arvatti/fonte-chaveada-buck/Fonte_Rev1.kicad_sch

## KiCad design Fonte_Rev1.kicad_sch (2026-03-06)

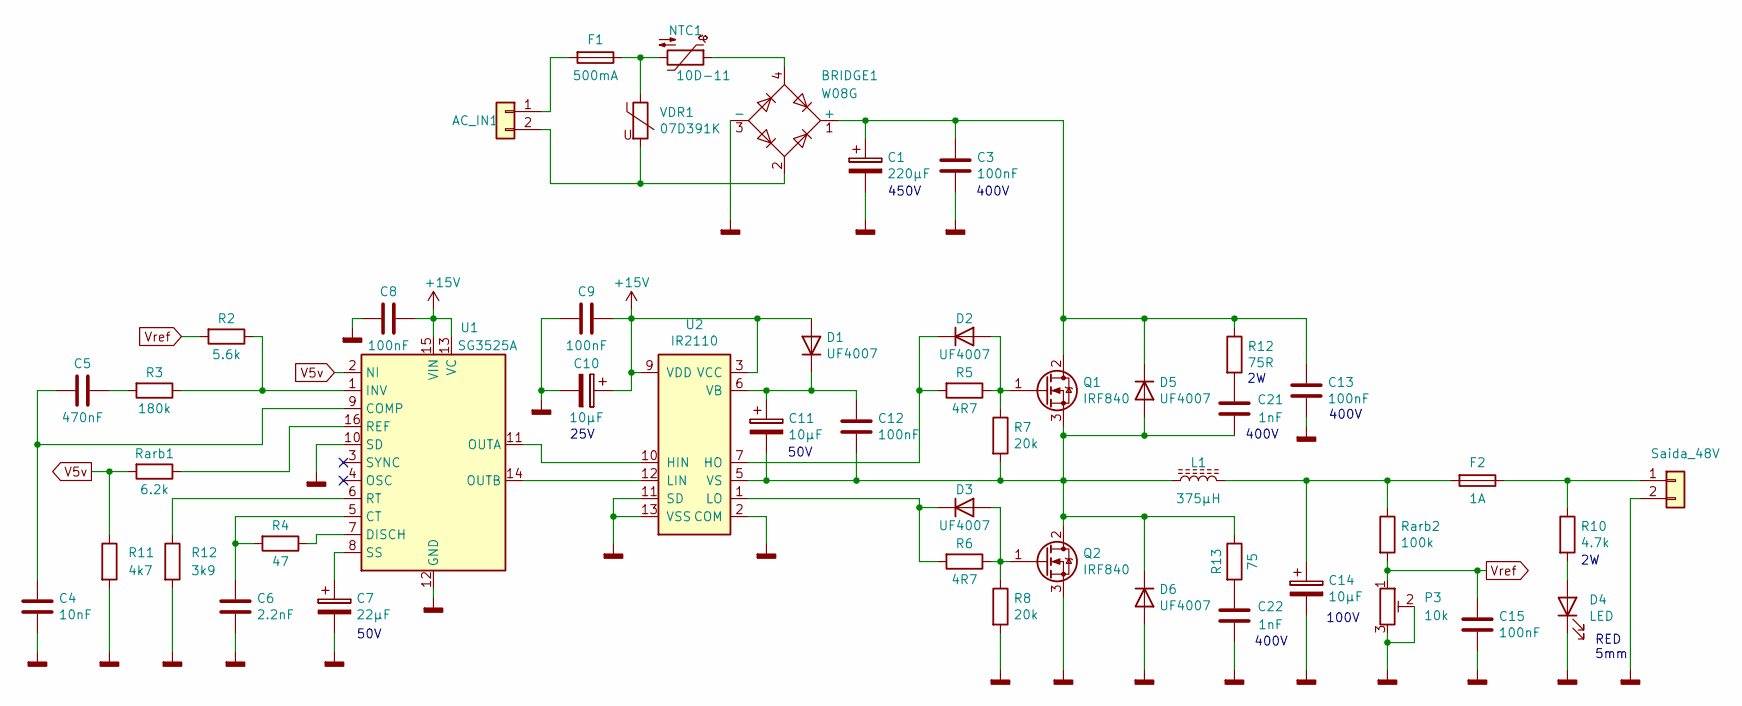
[picture p6: schematic Fonte_Rev1.kicad_sch]

Parts:
AC_IN1: Conn_01x02; PhoenixContact_GMSTBVA_2,5_2-G-7,62_1x02_P7.62mm_Vertical
BRIDGE1: W08G; Diode_Bridge_Round_D9.8mm
C1: 220µF; CP_Radial_D22.0mm_P10.00mm_SnapIn
C3, C13: 100nF; C_Rect_L11.0mm_W4.2mm_P10.00mm_MKT
C4: 10nF; C_Rect_L7.0mm_W2.0mm_P5.00mm
C5: 470nF; C_Rect_L7.0mm_W2.5mm_P5.00mm
C6: 2.2nF; C_Disc_D3.8mm_W2.6mm_P2.50mm
C7: 22µF; CP_Radial_D5.0mm_P2.50mm
C8, C9, C12, C15: 100nF; C_Rect_L7.0mm_W2.0mm_P5.00mm
C10, C11, C14: 10µF; CP_Radial_D5.0mm_P2.50mm
C21, C22: 1nF; C_Rect_L7.0mm_W2.0mm_P5.00mm
D1, D2, D3, D5, D6: UF4007; D_DO-41_SOD81_P10.16mm_Horizontal
D4: LED; LED_D4.0mm
F1: 500mA; fuse_20mm_PCB_clamp
F2: 1A; fuse_20mm_PCB_clamp
L1: 375µH; inductorEE20
NTC1: 10D-11; RV_Disc_D12mm_W3.9mm_P7.5mm
P3: 10k; Potentiometer_Bourns_3296W_Vertical
Q1, Q2: IRF840; TO-220-3_Vertical
R2: 5.6k; R_Axial_DIN0207_L6.3mm_D2.5mm_P10.16mm_Horizontal
R3: 180k; R_Axial_DIN0207_L6.3mm_D2.5mm_P10.16mm_Horizontal
R4: 47; R_Axial_DIN0207_L6.3mm_D2.5mm_P10.16mm_Horizontal
R5, R6: 4R7; R_Axial_DIN0207_L6.3mm_D2.5mm_P10.16mm_Horizontal
R7, R8: 20k; R_Axial_DIN0207_L6.3mm_D2.5mm_P10.16mm_Horizontal
R10: 4.7k; R_Axial_DIN0414_L11.9mm_D4.5mm_P15.24mm_Horizontal
R11: 4k7
R12: 75R; R_Axial_DIN0414_L11.9mm_D4.5mm_P15.24mm_Horizontal
R13: 75; R_Axial_DIN0414_L11.9mm_D4.5mm_P15.24mm_Horizontal
Rarb1: 6.2k; R_Axial_DIN0207_L6.3mm_D2.5mm_P10.16mm_Horizontal
Rarb2: 100k; R_Axial_DIN0207_L6.3mm_D2.5mm_P10.16mm_Horizontal
Saida_48V: Conn_01x02; PhoenixContact_GMSTBVA_2,5_2-G-7,62_1x02_P7.62mm_Vertical
U1: SG3525A; DIP-16_W7.62mm_LongPads
U2: IR2110; DIP-14_W7.62mm_LongPads
VDR1: 07D391K; RV_Disc_D7mm_W3.4mm_P5mm

Connections:
+15V: C8.1, C9.1, C10.1, D1.2 (A), U1.13 (VC), U1.15 (VIN), U2.3 (VCC), U2.9 (VDD)
GNDD: BRIDGE1.3 (-), C1.2, C3.2, C4.2, C6.2, C7.2, C8.2, C9.2, C10.2, C13.2, C14.2, C15.2, C22.1, D4.1 (K), D6.2 (A), P3.2, P3.3, Q2.3 (S), R8.2, R11.2, R12.2, Saida_48V.2, U1.10 (SD), U1.12 (GND), U2.2 (COM), U2.11 (SD), U2.13 (VSS)
unnamed: AC_IN1.1, F1.2
unnamed: AC_IN1.2, BRIDGE1.2, VDR1.2
unnamed: BRIDGE1.1 (+), C1.1, C3.1, C13.1, D5.1 (K), Q1.2 (D), R12.1
unnamed: BRIDGE1.4, NTC1.1
unnamed: C4.1, C5.2, U1.9 (COMP)
unnamed: C5.1, R3.2
unnamed: C6.1, R4.2, U1.5 (CT)
unnamed: C7.1, U1.8 (SS)
unnamed: C11.1, C12.1, D1.1 (K), U2.6 (VB)
unnamed: C11.2, C12.2, C21.1, D5.2 (A), D6.1 (K), L1.1, Q1.3 (S), Q2.2 (D), R7.2, R13.1, U2.5 (VS)
unnamed: C14.1, F2.2, L1.2, Rarb2.1
unnamed: C21.2, R12.2
unnamed: C22.2, R13.2
unnamed: D2.1 (K), R5.2, U2.7 (HO)
unnamed: D2.2 (A), Q1.1 (G), R5.1, R7.1
unnamed: D3.1 (K), R6.2, U2.1 (LO)
unnamed: D3.2 (A), Q2.1 (G), R6.1, R8.1
unnamed: D4.2 (A), R10.2
unnamed: F1.1, NTC1.2, VDR1.1
unnamed: F2.1, R10.1, Saida_48V.1
unnamed: R2.1, R3.1, U1.1 (INV)
unnamed: R4.1, U1.7 (DISCH)
unnamed: R12.1, U1.6 (RT)
unnamed: Rarb1.1, U1.16 (REF)
unnamed: U1.11 (OUTA), U2.10 (HIN)
unnamed: U1.14 (OUTB), U2.12 (LIN)
V5v: R11.1, Rarb1.2, U1.2 (NI)
Vref: C15.1, P3.1, R2.2, Rarb2.2

Notes on the sheet:
50V
25V
450V
400V
100V
RED 5mm
